qkarthi/iotRemoteSwitch/ConfigStore.h

struct ConfigStore {
  uint32_t  magic;
  char      version[9];
  uint8_t   flagConfig: 1;
  uint8_t   flagApFail: 1;
  uint8_t   flagSelfTest: 1;

  char      wifiSSID[34];
  char      wifiPass[34];

  char      cloudToken[34];
  char      cloudHost[34];
  uint16_t  cloudPort;

  char      equip_name[34];

  char      device_1_name[24]; //dev1
  char      device_2_name[24]; //dev2


  uint8_t   Dev_1_state: 1;
  uint8_t   Dev_2_state: 1;


  uint8_t   Dev_1_swi: 1;
  uint8_t   Dev_2_swi: 1;

  uint8_t   upnp_vars: 1;

  uint16_t  checksum;
} __attribute__((packed));

ConfigStore configStore;

const ConfigStore configDefault = {
  0x626C6E6B,
  BOARD_FIRMWARE_VERSION,
  0, 0, 0,

  "",
  "",

  "invalid token",
  "blynk-cloud.com", 80,
  "switcher",
  "appliance1", "appliance2",
  0, 0,
  0, 0,
  0,
  0
};

#include <EEPROM.h>
#define EEPROM_CONFIG_START 0

void config_load()
{
  memset(&configStore, 0, sizeof(configStore));
  EEPROM.get(EEPROM_CONFIG_START, configStore);
  if (configStore.magic != configDefault.magic) {
    DEBUG_PRINT("Using default config.");
    configStore = configDefault;
    return;
  }
}

bool config_save()
{
  EEPROM.put(EEPROM_CONFIG_START, configStore);
  EEPROM.commit();
  return true;
}

bool config_init()
{
  EEPROM.begin(sizeof(ConfigStore));
  config_load();
  return true;
}

void enterResetConfig()
{
  DEBUG_PRINT("Resetting configuration!");
  configStore = configDefault;
  config_save();
  BlynkState::set(MODE_WAIT_CONFIG);
}

template<typename T, int size>
void CopyString(const String& s, T(&arr)[size]) {
  s.toCharArray(arr, size);
}
